gruenst/PVsec2026/01.JPG

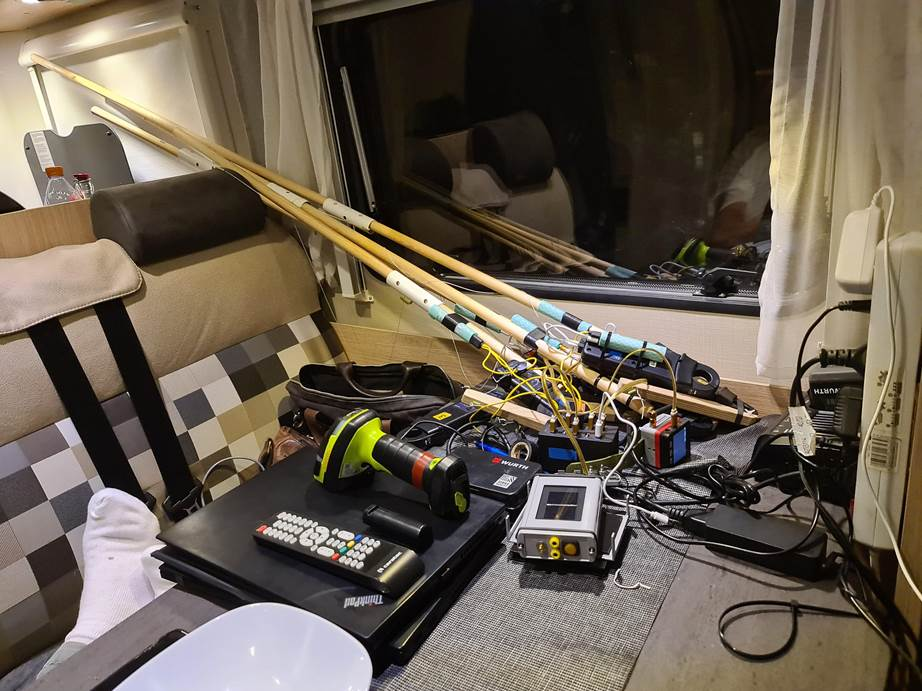
01.JPG
