gruenst/PVsec2026/01_MainUnit/01_ESP32/05_images/001.JPG

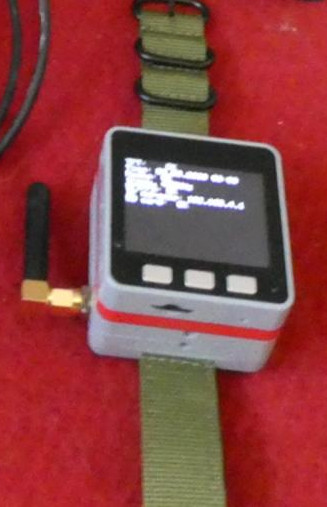
01_MainUnit/01_ESP32/05_images/001.JPG
