gruenst/PVsec2026/01_MainUnit/01_ESP32/05_images/P1020794.JPG

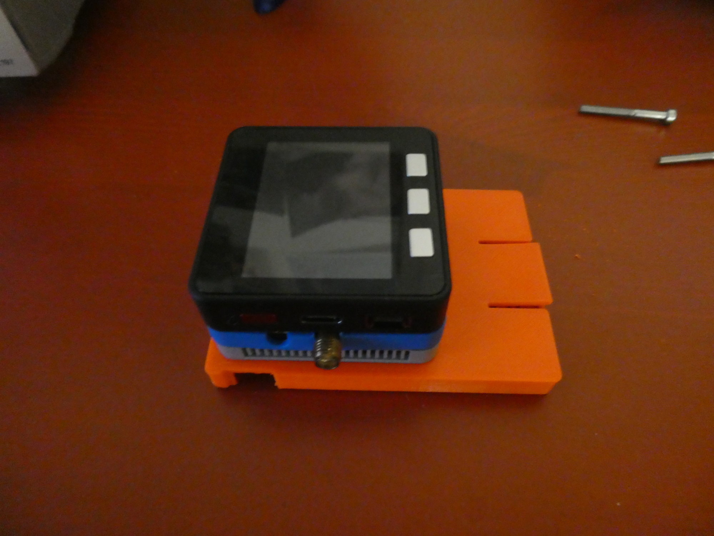
01_MainUnit/01_ESP32/05_images/P1020794.JPG
