gruenst/PVsec2026/01_MainUnit/02_USB_LORA/05_images/DSC_0191.JPG

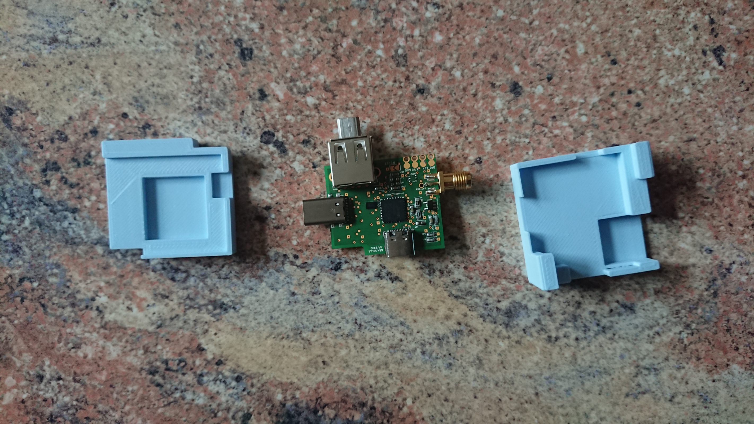
01_MainUnit/02_USB_LORA/05_images/DSC_0191.JPG
