gruenst/PVsec2026/01_MainUnit/02_USB_LORA/05_images/DSC_0192.JPG

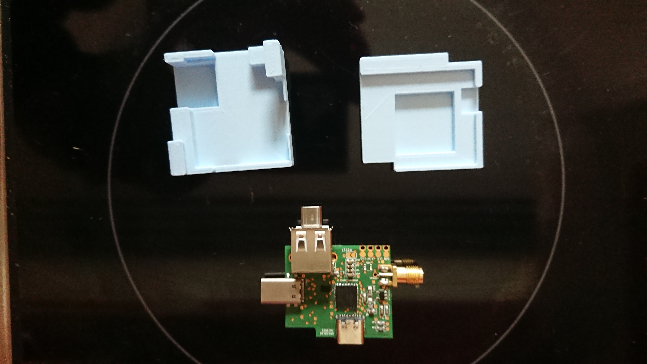
01_MainUnit/02_USB_LORA/05_images/DSC_0192.JPG
