gruenst/PVsec2026/02.JPG

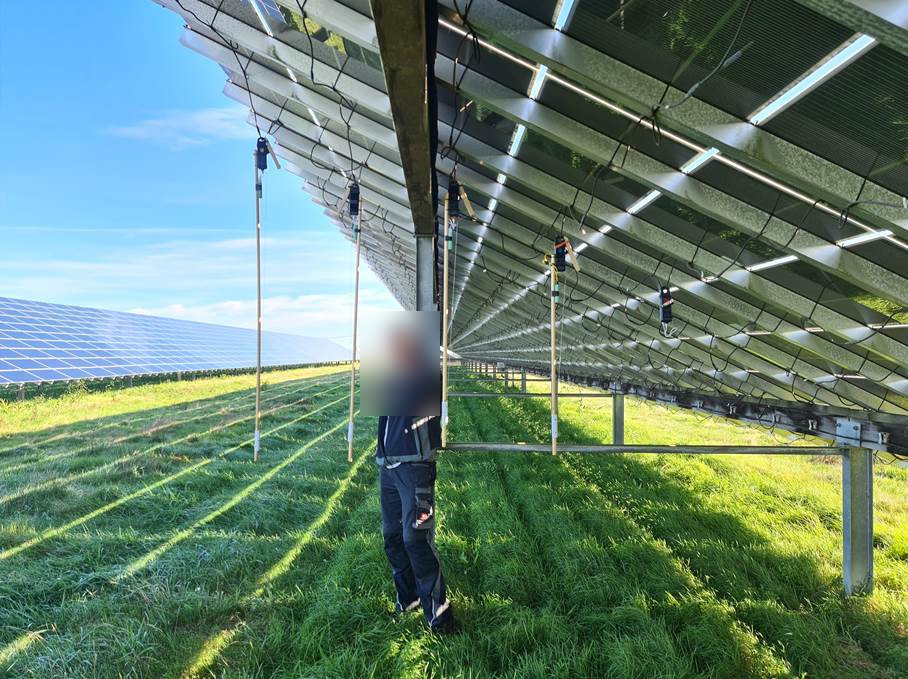
02.JPG
