gruenst/PVsec2026/02_CurrentClamp/04_3Dprint/CIMG1478.JPG

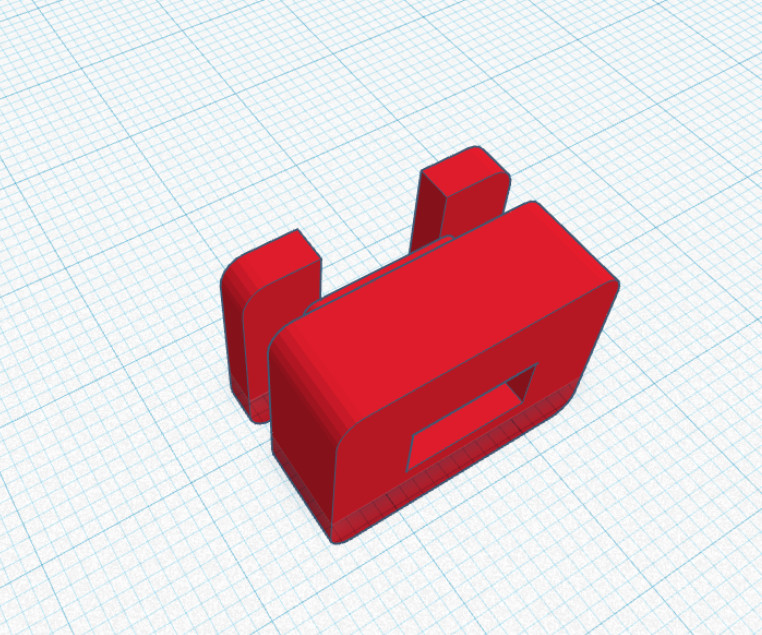
02_CurrentClamp/04_3Dprint/CIMG1478.JPG
