gruenst/PVsec2026/02_CurrentClamp/05_images/CIMG1180.JPG

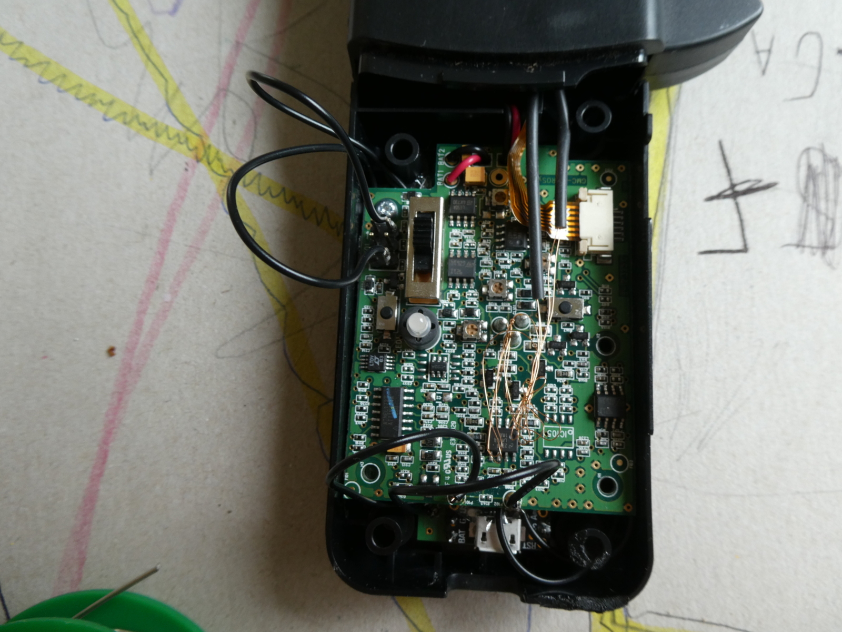
02_CurrentClamp/05_images/CIMG1180.JPG
