gruenst/PVsec2026/02_CurrentClamp/05_images/CIMG1480.JPG

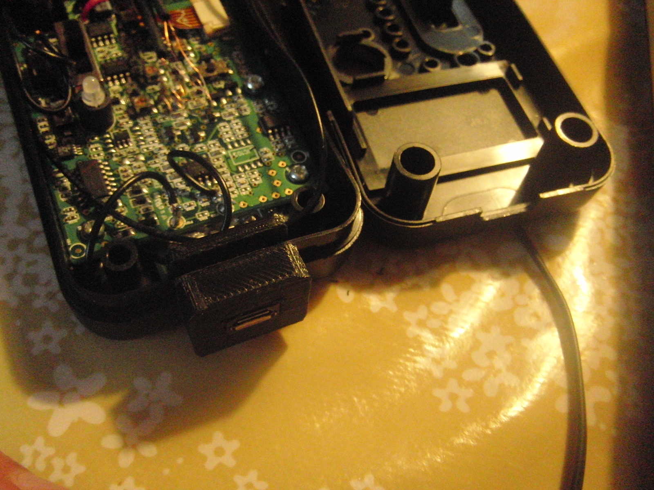
02_CurrentClamp/05_images/CIMG1480.JPG
