gruenst/PVsec2026/02_CurrentClamp/05_images/CIMG1482.JPG

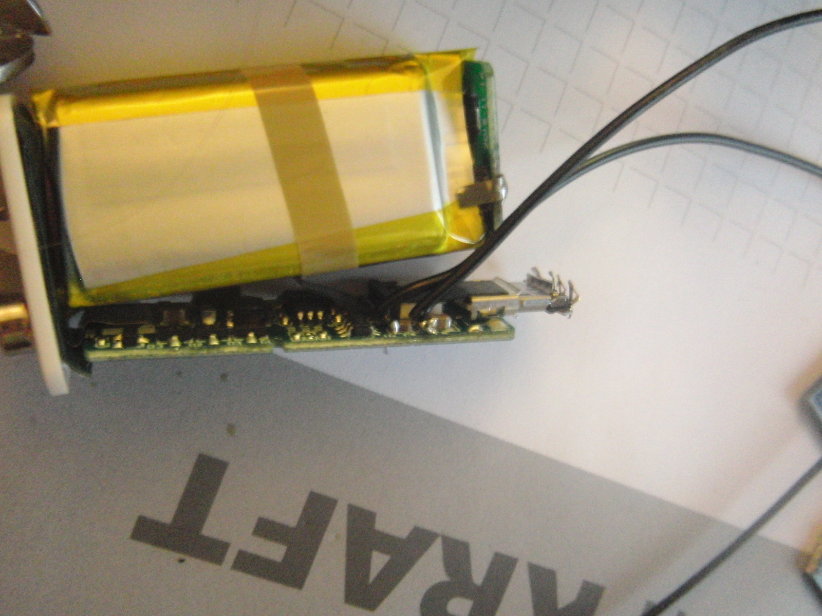
02_CurrentClamp/05_images/CIMG1482.JPG
