gruenst/PVsec2026/02_CurrentClamp/05_images/CIMG1486.JPG

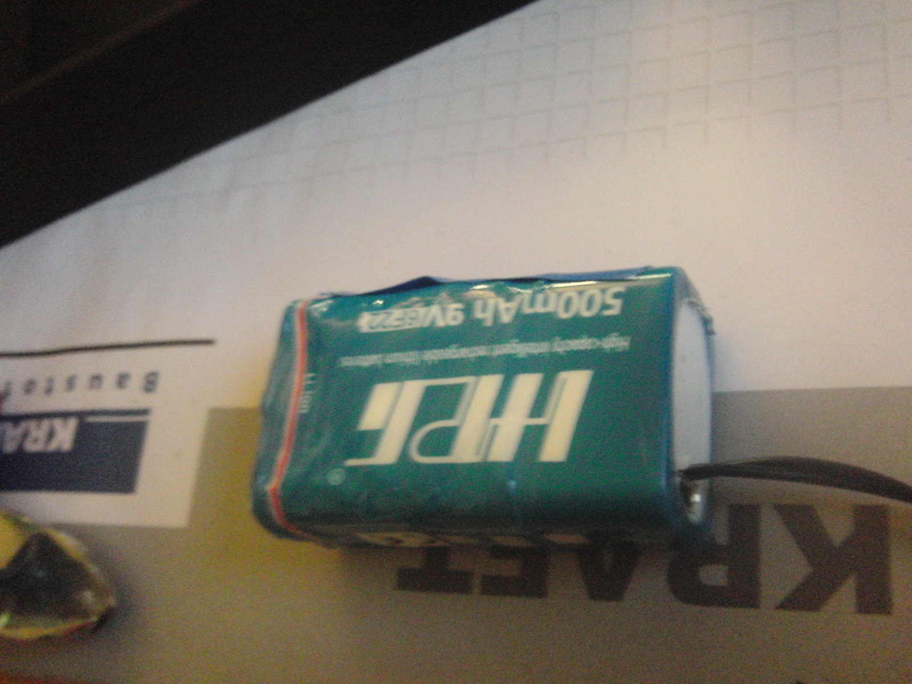
02_CurrentClamp/05_images/CIMG1486.JPG
