gruenst/PVsec2026/02_CurrentClamp/05_images/CIMG1569.JPG

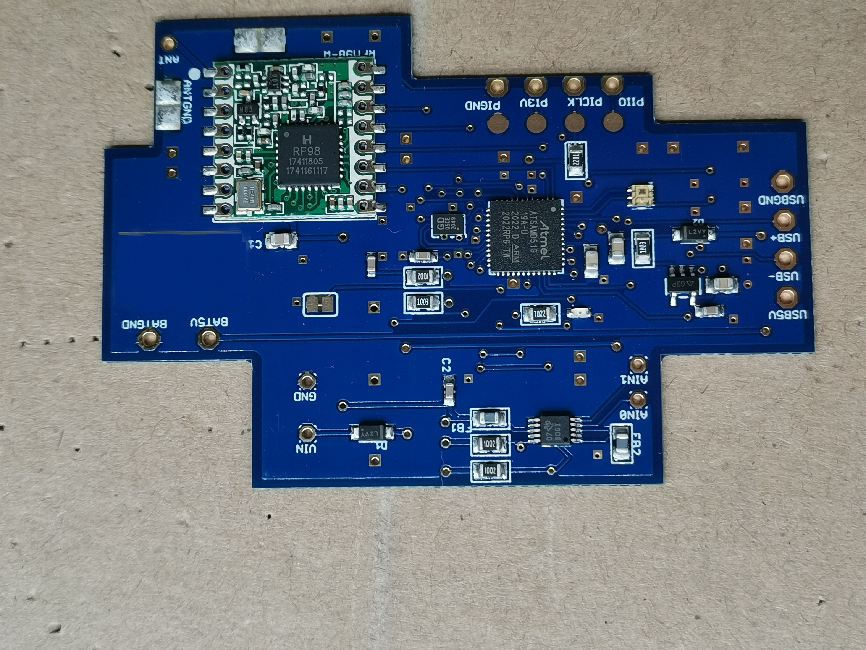
02_CurrentClamp/05_images/CIMG1569.JPG
