gruenst/PVsec2026/02_CurrentClamp/05_images/CIMG1570.JPG

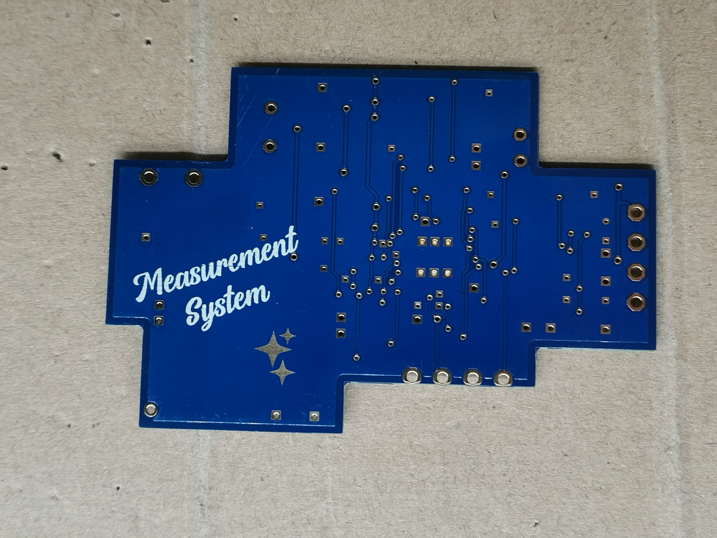
02_CurrentClamp/05_images/CIMG1570.JPG
