gruenst/PVsec2026/03_IrradianceTemp/01_PCB/board.png

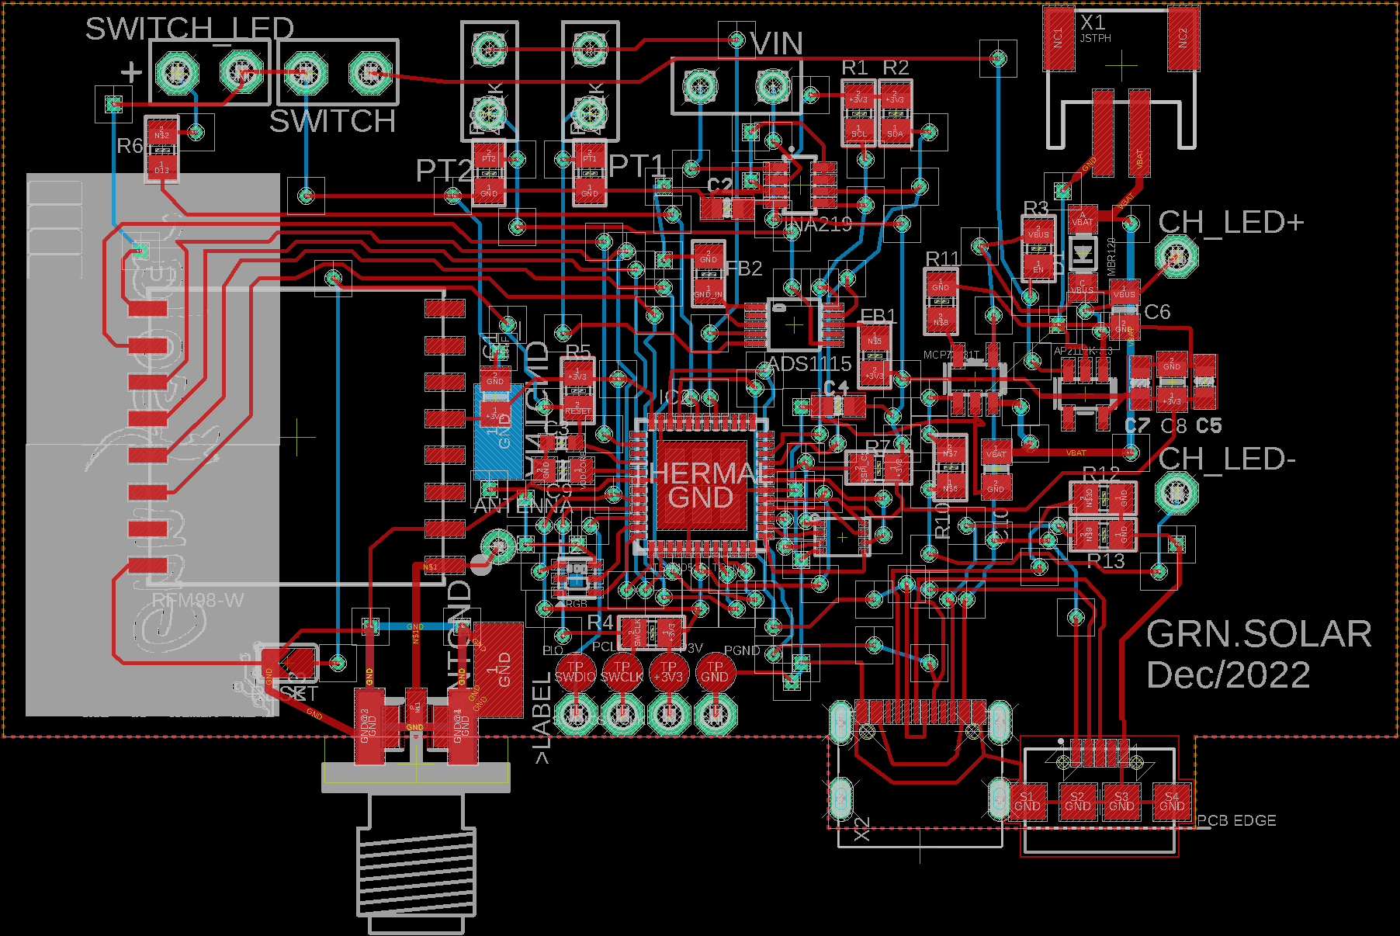
03_IrradianceTemp/01_PCB/board.png
