gruenst/PVsec2026/03_IrradianceTemp/05_images/004.JPG

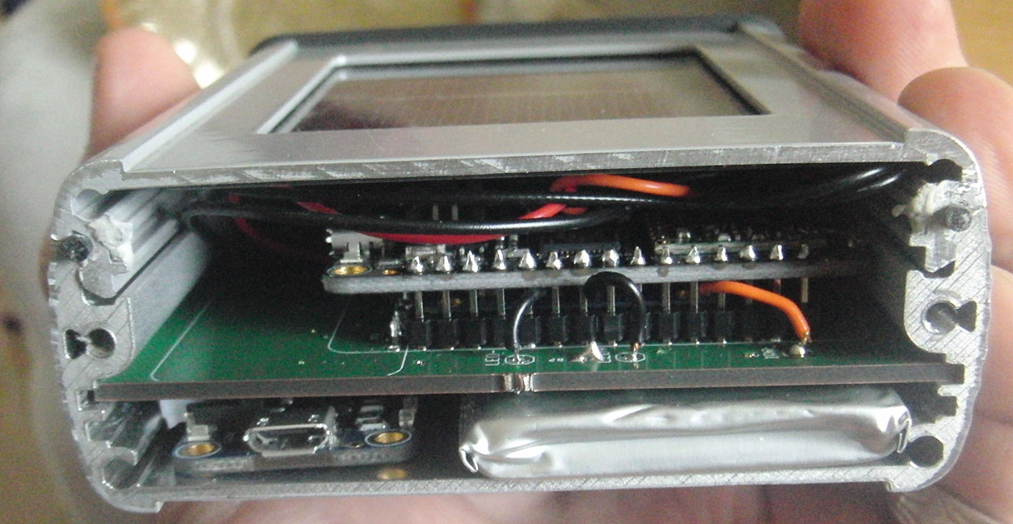
03_IrradianceTemp/05_images/004.JPG
