gruenst/PVsec2026/04.JPG

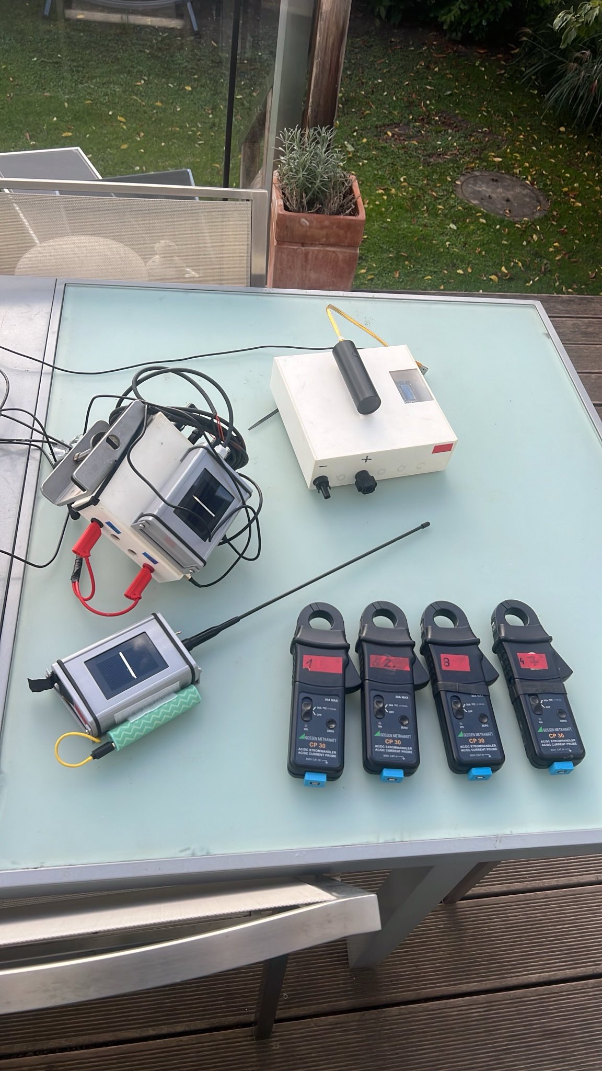
04.JPG
