gruenst/PVsec2026/04_Voltage/01_PCB/image.png

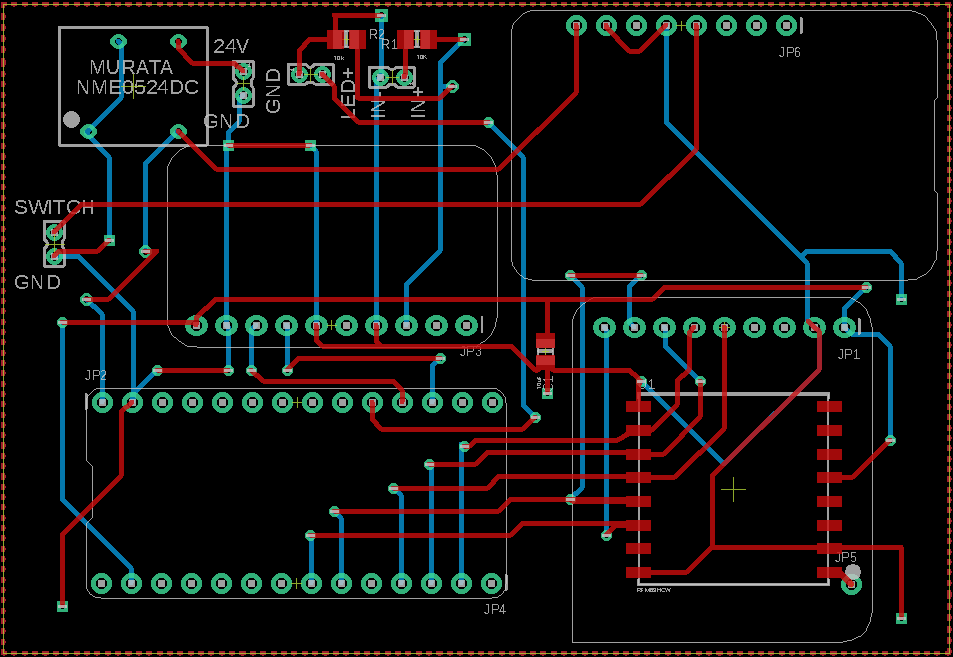
04_Voltage/01_PCB/image.png
