gruenst/PVsec2026/04_Voltage/04_3Dprint/case.png

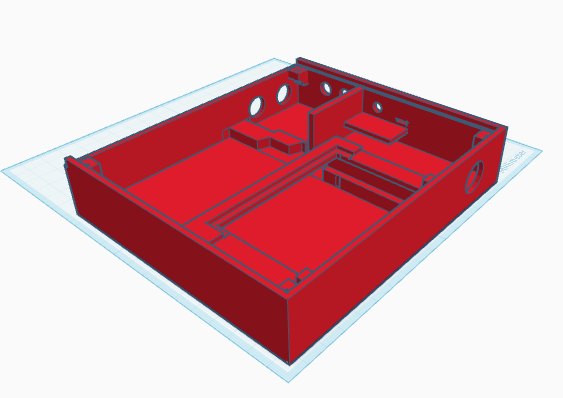
04_Voltage/04_3Dprint/case.png
