gruenst/PVsec2026/04_Voltage/05_images/CIMG1509.JPG

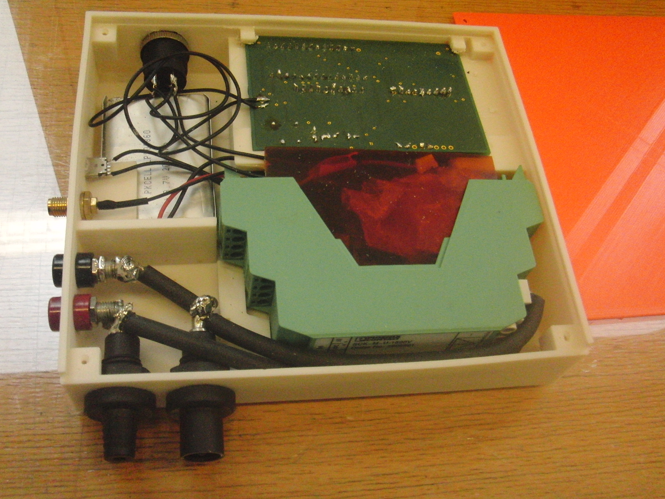
04_Voltage/05_images/CIMG1509.JPG
