gruenst/PVsec2026/04_Voltage/05_images/CIMG1510.JPG

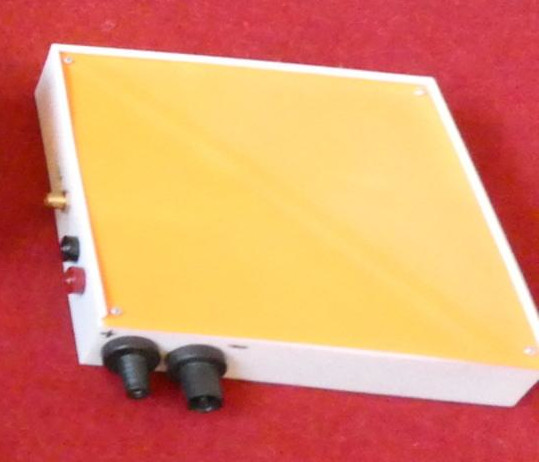
04_Voltage/05_images/CIMG1510.JPG
